Meo98/picostack/tools/sch/versorgung.py

# -*- coding: utf-8 -*-
"""Die Versorgungszelle: Verpolschutz, TVS, 5V-Regler, VSYS-Diode.

Implementiert woertlich stack_spec.VERSORGUNG (Task 3, PicoStack v2):

    schutz_drain_an = "PWR_IN"        -- Q90-Drain an der Einspeisung
    gate_teiler_an  = "+24V_LOKAL"    -- R90/R91-Teiler an der lokalen Schiene
    vsys_diode      = True            -- D91 vor VSYS
    eingang_v       = (6.0, 30.0)     -- Eingangsfenster des Reglers U90

DER V1-FEHLER, DEN DIESE ZELLE BEHEBT. tools/sch/motormodul.py
(`_endstufe_leistung()`, Q1/R11/R12, aus dem Altprojekt uebernommen)
schaltete den P-Kanal-Verpolschutz genau umgekehrt: Q1s SOURCE lag an
der rohen Einspeisung ("PWR24V"), Q1s DRAIN an der bereits geschuetzten,
lokalen Schiene ("+24V") -- und der Gate-Teiler (R11/R12) haengt dort
ebenfalls an PWR24V, nicht an der lokalen Schiene. Bei einer P-Kanal-
Schutzschaltung ist die Reihenfolge kein Geschmacksdetail:

  * Ein MOSFET hat eine parasitaere Body-Diode zwischen Source und
    Drain, die in der Sperrichtung des Kanals ohnehin leitet (beim
    P-Kanal-Typ: Anode am Drain, Kathode an Source). Sitzt die Source
    an der Einspeisung, leitet diese Body-Diode bei VERPOLTER
    Einspeisung direkt in die lokale Schiene durch -- der Transistor
    kann das gar nicht verhindern, er wird von seiner eigenen Diode
    umgangen.
  * Zusaetzlich haengt in der v1-Schaltung die TVS-Diode (D1) an der
    JETZT vorwaertsgespeisten lokalen Schiene. Bei verpolter
    Einspeisung wird sie DURCH die leitende Body-Diode in
    Durchlassrichtung betrieben und leitet ihrerseits kraeftig --
    zusammen bilden Body-Diode und TVS einen Kurzschluss-Pfad
    ("Crowbar") von der verpolten Einspeisung nach Masse, statt den
    Rueckstrom zu sperren. Der Schutz schuetzt in genau dem Fall nichts,
    fuer den er gedacht ist.

RICHTIGE TOPOLOGIE (diese Datei, Q90/R90/R91):
  * Q90-Drain (Pin 2) an PWR_IN (der rohen Einspeisung, VOR jedem
    eigenen Schutz/Regler) -- die Body-Diode zeigt jetzt so, dass sie
    bei verpolter Einspeisung SPERRT (Anode am Drain/PWR_IN, das bei
    Verpolung negativ liegt; Kathode an Source/+24V), statt
    durchzuschalten.
  * Q90-Source (Pin 3) an +24V (der lokalen, bereits geschuetzten
    Schiene) -- alles, was danach kommt (D90, C90, U90 und jeder
    Verbraucher der Zelle, die diese Schiene bezieht), liegt HINTER dem
    Schutz.
  * Gate-Teiler R90 (Gate<->+24V) UND R91 (Gate<->GND) haengen an der
    LOKALEN Schiene, nicht an PWR_IN: haenge R90 stattdessen an PWR_IN,
    koennte eine verpolte Einspeisung das Gate direkt falsch ansteuern
    (Source auf +24V waere dann ueber R90 mit dem NEGATIVEN PWR_IN
    verbunden, VGS wird stark positiv -- bei einem P-Kanal-MOSFET
    schaltet das den Kanal AUS, gerade wenn er am dringendsten sperren
    soll) und den Schutz umgehen, den er gerade herstellen soll --
    exakt der Fall, den stack_spec.VERSORGUNG["gate_teiler_an"] =
    "+24V_LOKAL" ausschliesst.

tests/test_versorgung.py haelt die vier Kern-Pruefungen des Task-3-
Briefs UND einen Rot-Nachweis fest, der denselben Drain-Check
tatsaechlich gegen die generierte motormodul.py-Netzliste laufen laesst
und dort bestaetigt, dass er (Stand vor dieser Etappe) fehlschlaegt.

Herkunft der Bauteil-Muster (Task-3-Brief, woertlich uebernommen):
  * FP_KLEMME_2 (KF350/PT-1,5-3.5mm-Klemmen-Footprint) aus
    tools/sch/dimmermodul.py.
  * FP_SMC ("Diode_SMD:D_SMC", das MASCHINELLE Padset, nicht die
    Handloet-Variante) ebenfalls aus dimmermodul.py -- dort auch die
    SS36C-"C" vs. SS36-"SMA"-Unterscheidung dokumentiert.
  * Q_PMOS_GDS (generisches P-Kanal-Symbol, Pins 1=G/2=D/3=S) und
    FP_TO252 aus tools/sch/motormodul.py/sockelplatine.py.
  * FP_RECOM + die K7805-1000R3-Herleitung (NACHTRAG 2026-09-07) aus
    tools/sch/sockelplatine.py -- unten woertlich uebernommen, weil
    dieselbe Bauteilentscheidung (abgekuendigter 2-A-Typ, Ersatz durch
    den 1-A-Bruder derselben Baureihe) hier genauso gilt.
"""
import os
import sys
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
